theCheeese/Color-Pen-Reader/Presentations/Original Proposal Presentation.pptx

## AUTONOMOUS COLOR PEN READER

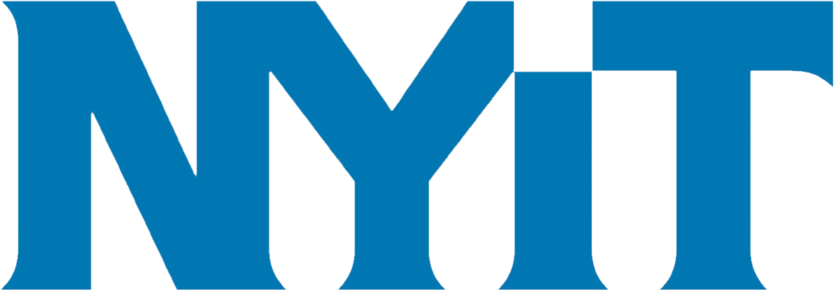
[picture p39: figure]

Capstone project proposal | Fall 2017

## 1. INTRODUCTION

1

Our members, motivations, significance and existing technologies

## Team members

MICHAEL MORDKOVICH (MISHA SYROV)
Project Manager/Software/Hardware Engineer

HAORAN WU (STEVEN WU)
Hardware/Software Engineer

KAIXIAN ZHU (ELLIS ZHU)
Software Engineer

OLUWADARASIMI ADENIYI (DARA ADENIYI)
Project Manager/Hardware Engineer/Researcher

Notes: This domain has controls around safeguarding assets. Some of the controls that this domain deals with are around the inventory of assets, ownership of assets, acceptable use of assets, return of assets.

It suggests controls around maintaining an inventory of assets and whether that inventory is current and kept up to date.

Also, it suggests that all information assets must have a clearly defined owner who is aware of their responsibilities.

It suggests that there be an acceptable use policy in place and there is process in place by which all employees are made aware of such policies.

## Existing technologies

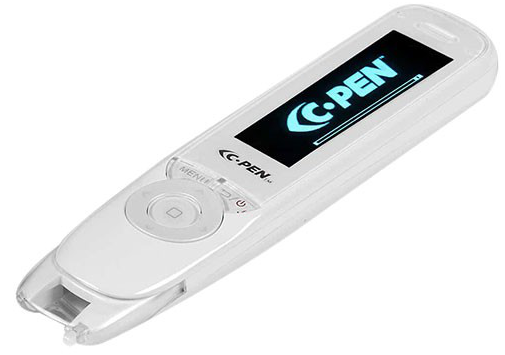
[picture p40: figure]
Resultado de imagem para cpen reader

- Existing technologies such as Scan marker and C-Pen don’t read colored text on colored backgrounds well

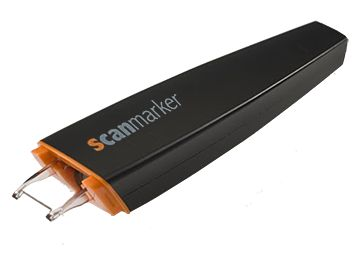
[picture p41: figure]
Resultado de imagem para scan marker logo

Notes: This domain has controls around safeguarding assets. Some of the controls that this domain deals with are around the inventory of assets, ownership of assets, acceptable use of assets, return of assets.

It suggests controls around maintaining an inventory of assets and whether that inventory is current and kept up to date.

Also, it suggests that all information assets must have a clearly defined owner who is aware of their responsibilities.

It suggests that there be an acceptable use policy in place and there is process in place by which all employees are made aware of such policies.

## 2. SOLUTION DEVELOPMENT

2

Solution proposal and plan of action

## Proposed solution

An electronic image processor that filters out the raw information from the pen reader's scanner

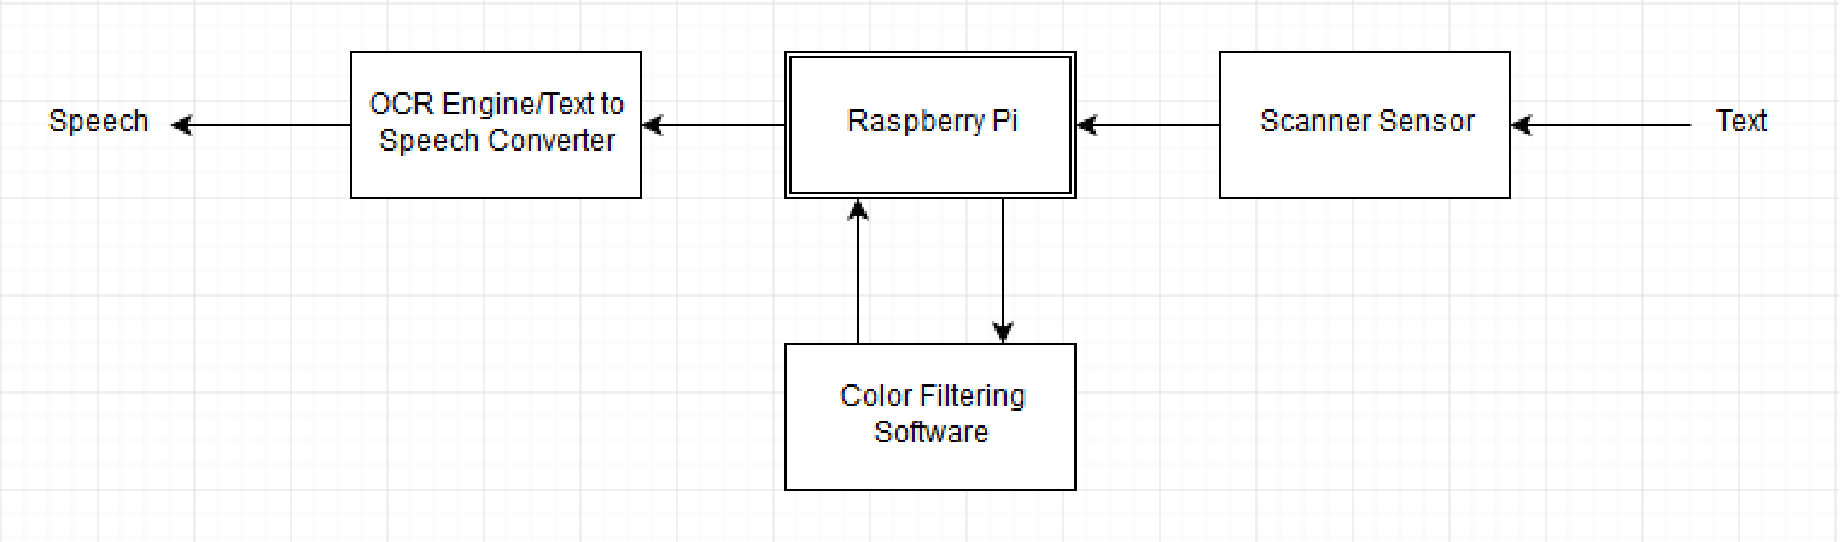
[picture p42: figure]

Notes: This domain has controls around safeguarding assets. Some of the controls that this domain deals with are around the inventory of assets, ownership of assets, acceptable use of assets, return of assets.

It suggests controls around maintaining an inventory of assets and whether that inventory is current and kept up to date.

Also, it suggests that all information assets must have a clearly defined owner who is aware of their responsibilities.

It suggests that there be an acceptable use policy in place and there is process in place by which all employees are made aware of such policies.

## Plan of action

Color filtering diagram:

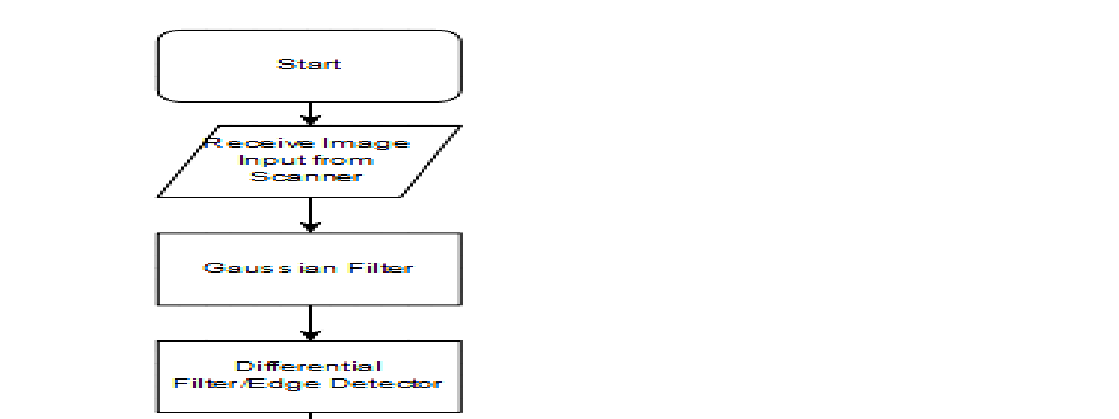
[picture p43: figure]
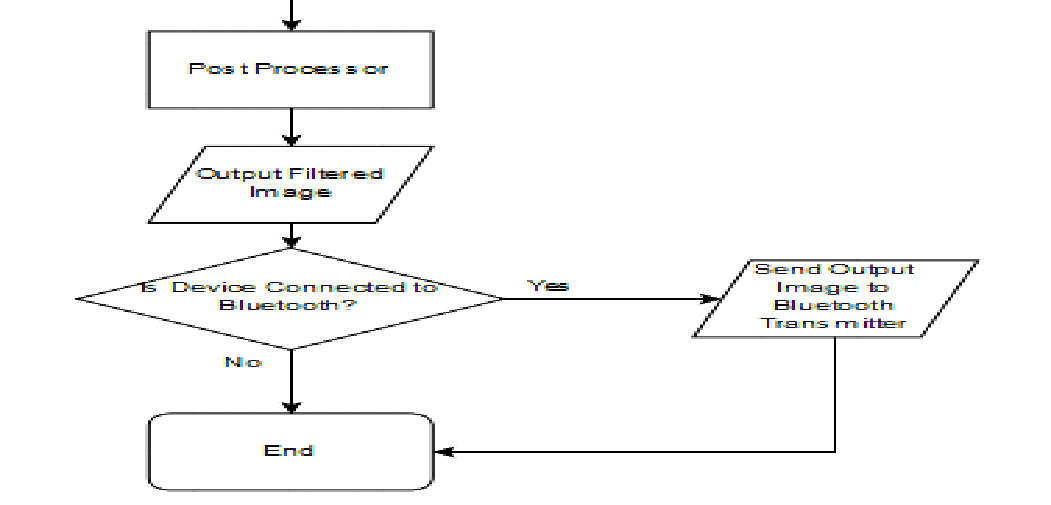
[picture p44: figure]

Notes: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

## Plan of action

Robotic Arm Control Diagram:

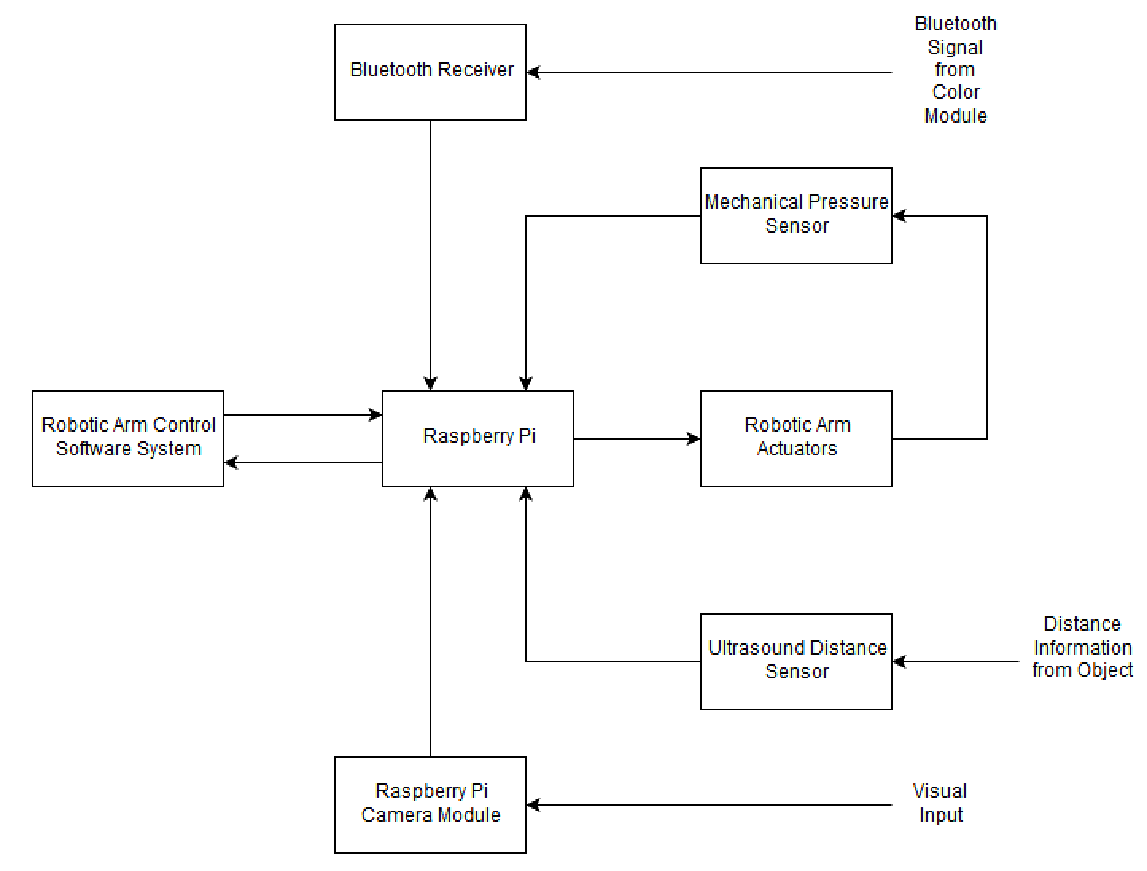
[picture p45: figure]

Notes: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

## Plan of action

Robot Arm Control Software Workflow:

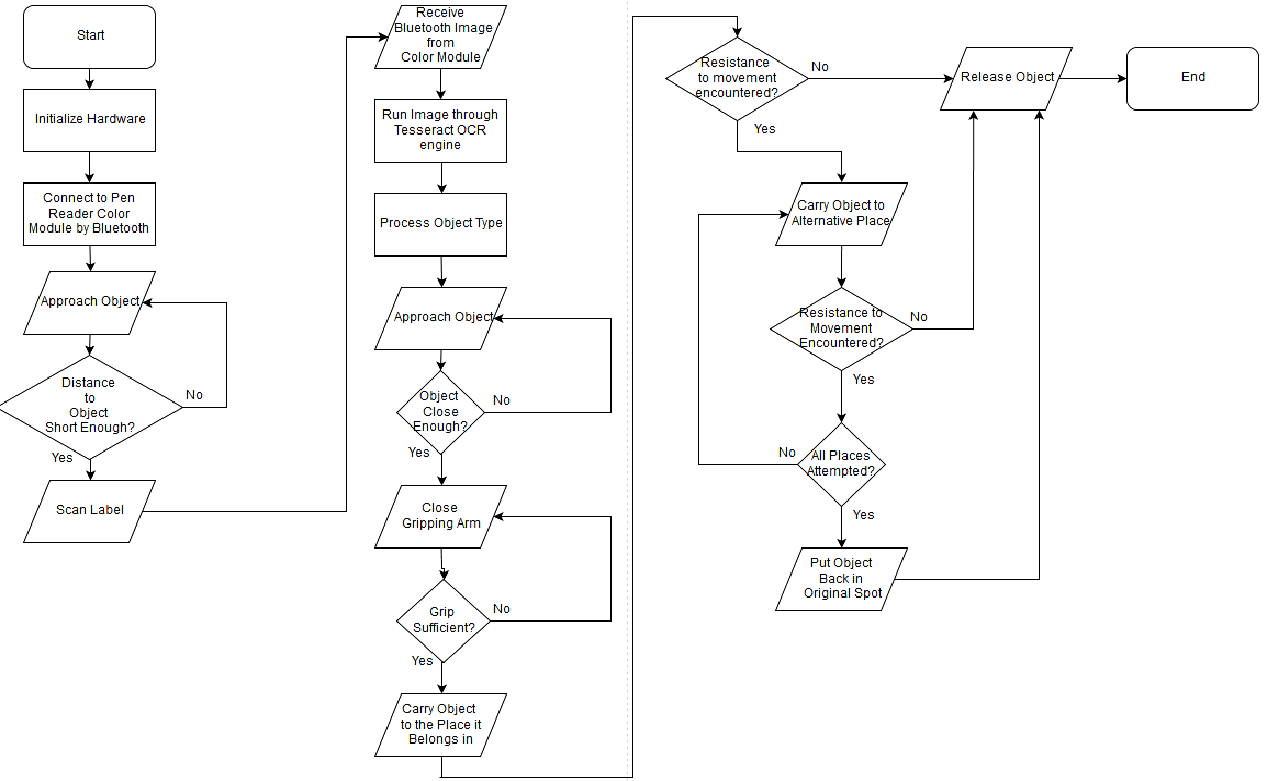
[picture p46: figure]

Notes: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

## Simulations

Input: Mixed colors, High, Medium & Low Resolution.

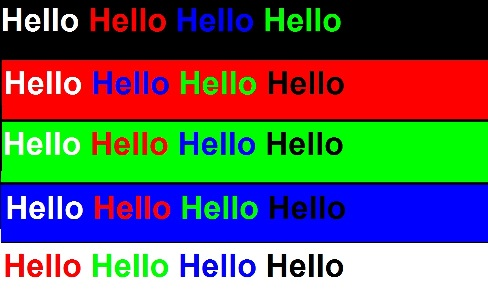
[picture p47: figure]
A close up of a screen Description generated with high confidence

Notes: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

## Simulations

Sobel Filter

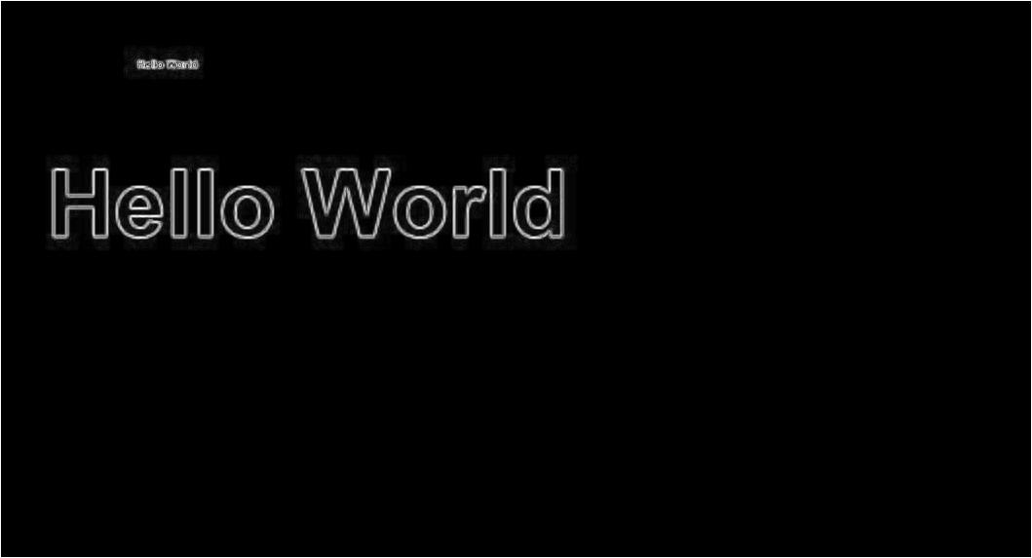
[picture p48: figure]
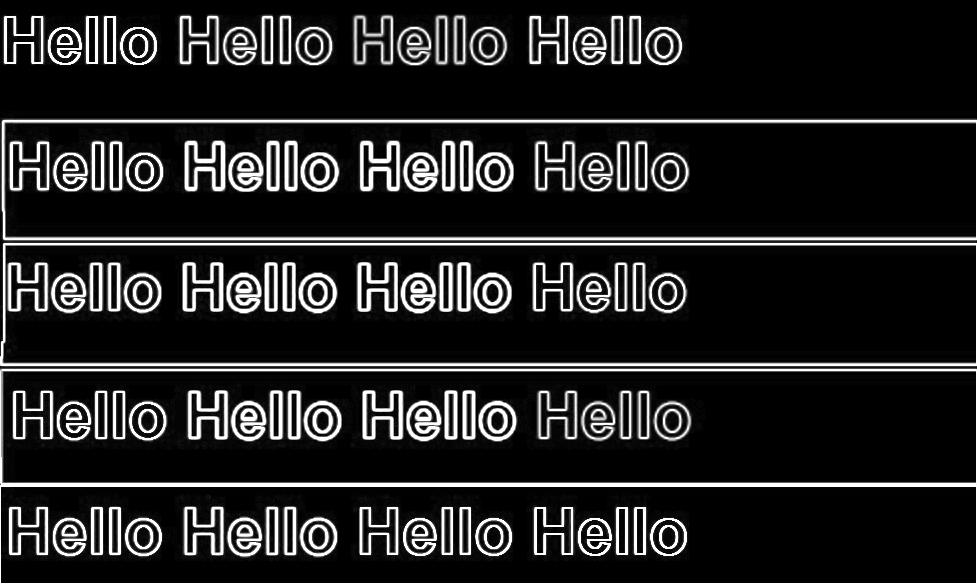
[picture p49: figure]
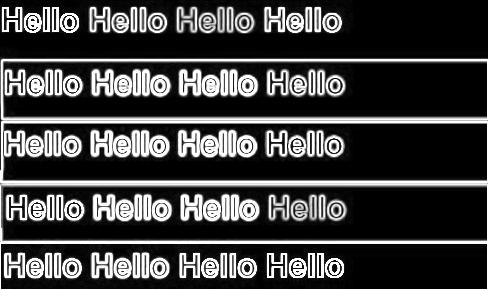
[picture p50: figure]
A screenshot of a cell phone Description generated with high confidence

Notes: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

## Simulations

Cosine Similarity Method

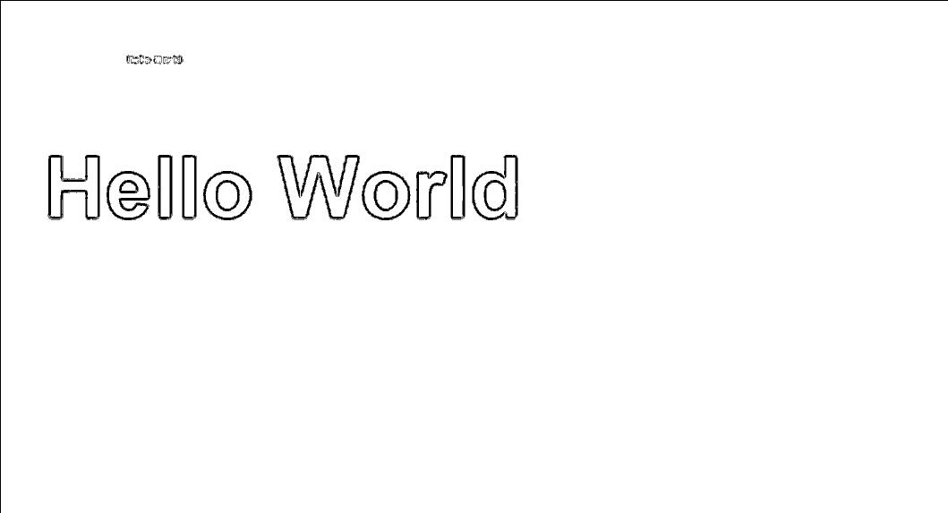
[picture p51: figure]
A screenshot of a cell phone Description generated with very high confidence
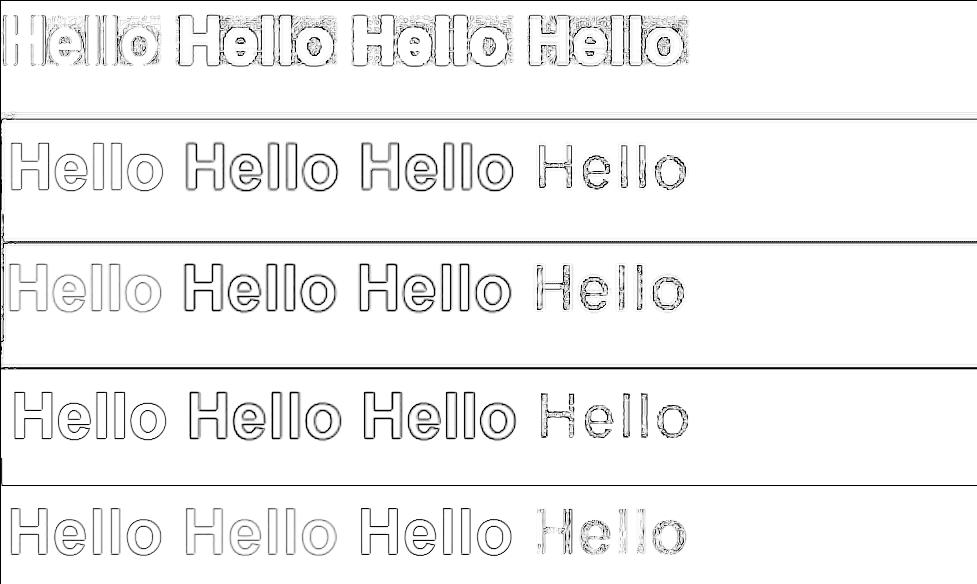
[picture p52: figure]
A screenshot of a cell phone Description generated with very high confidence
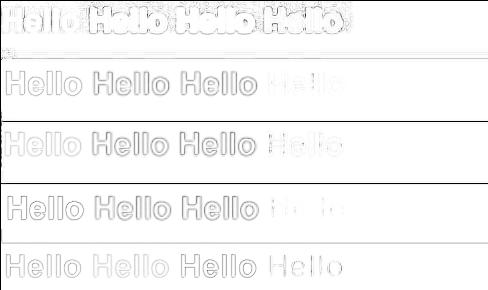
[picture p53: figure]
A screenshot of a cell phone Description generated with very high confidence

Notes: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

## Simulations

Canny and Sobel filters

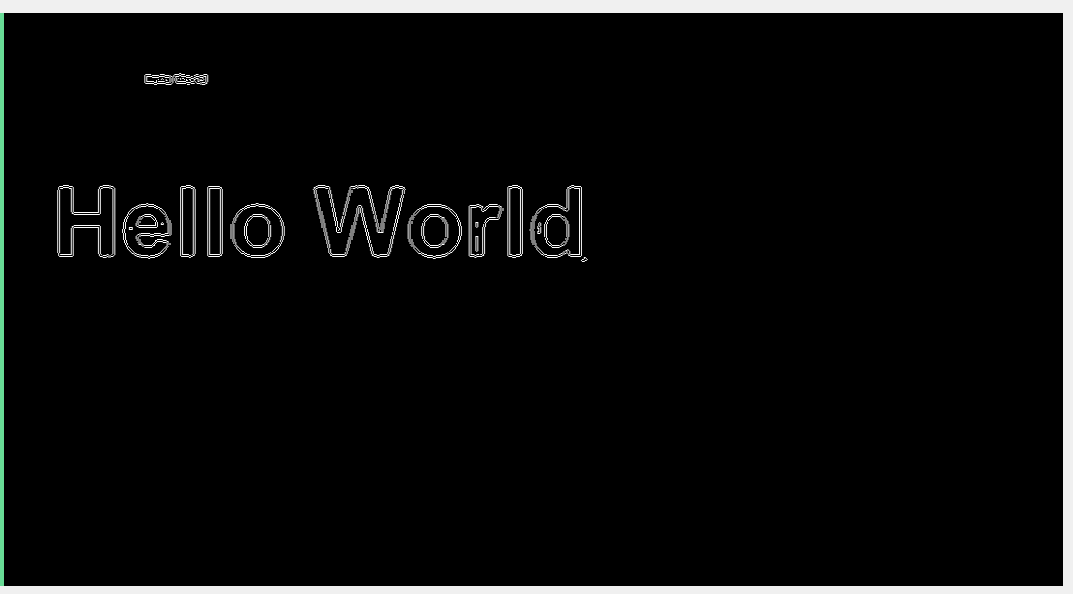
[picture p54: figure]
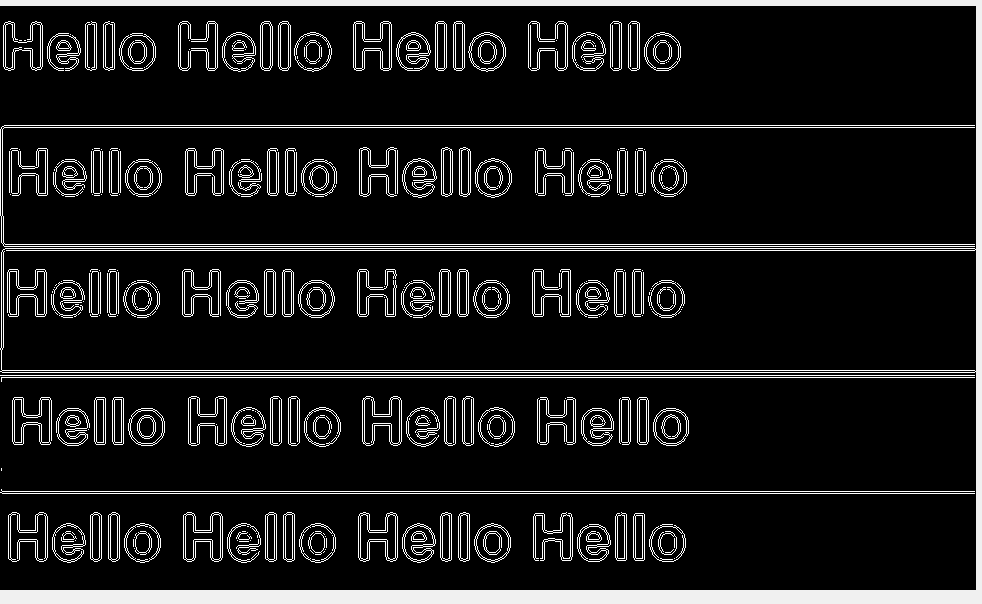
[picture p55: figure]
A picture containing text Description generated with high confidence
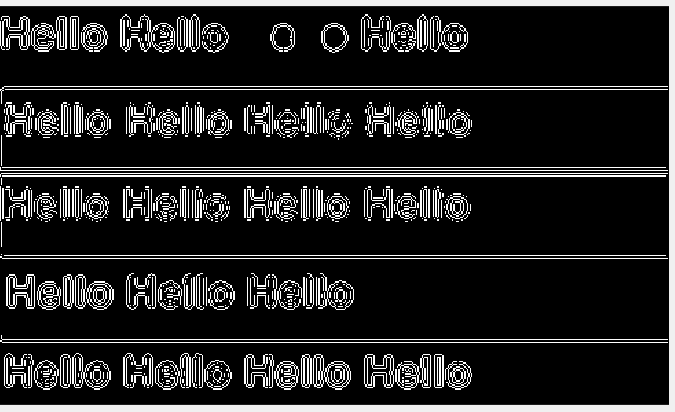
[picture p56: figure]
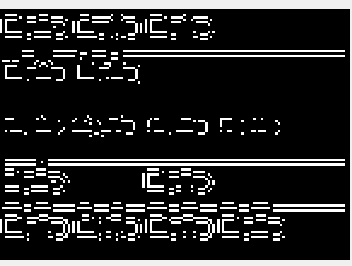
[picture p57: figure]

Notes: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

## Simulations

Canny Edge Detection Method

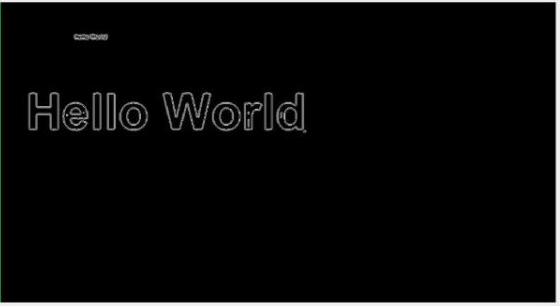
[picture p58: figure]
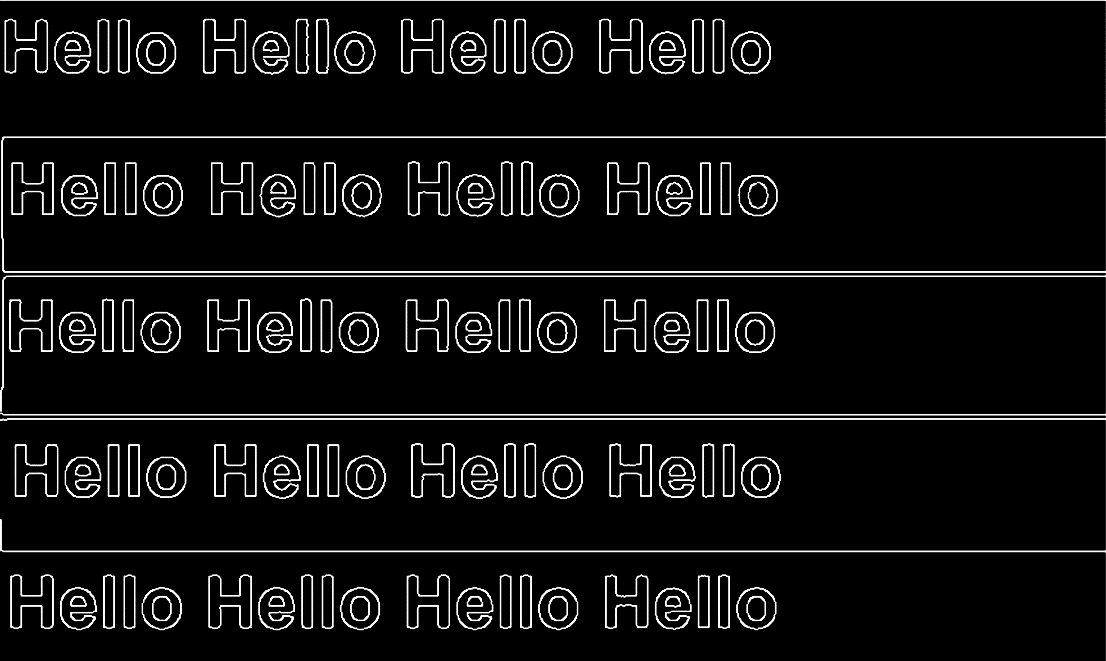
[picture p59: figure]
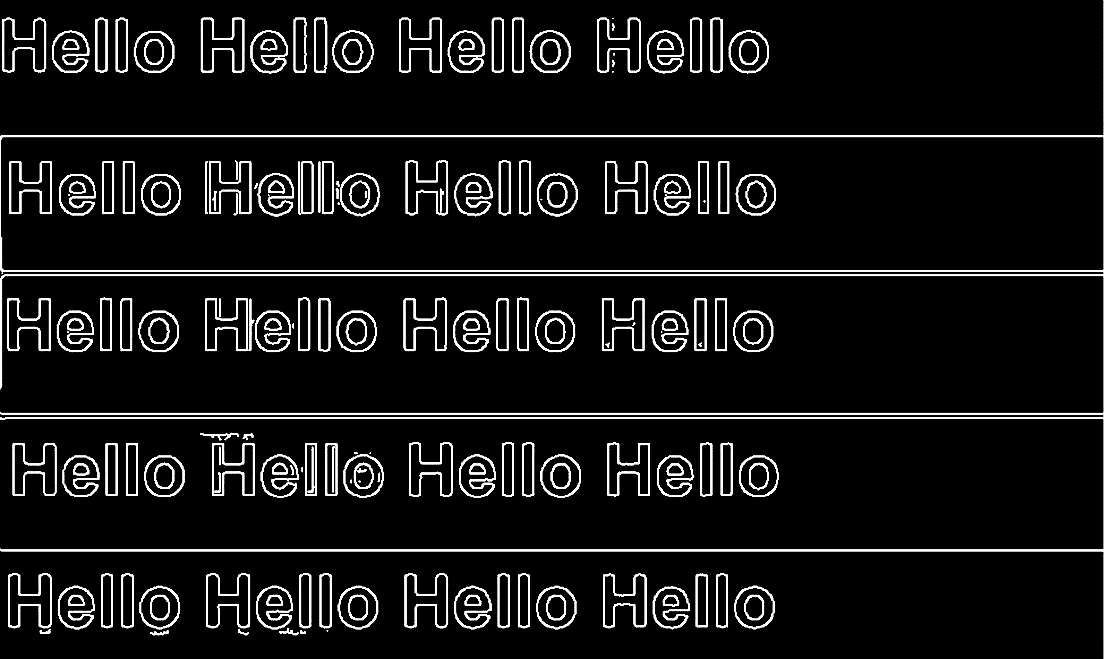
[picture p60: figure]
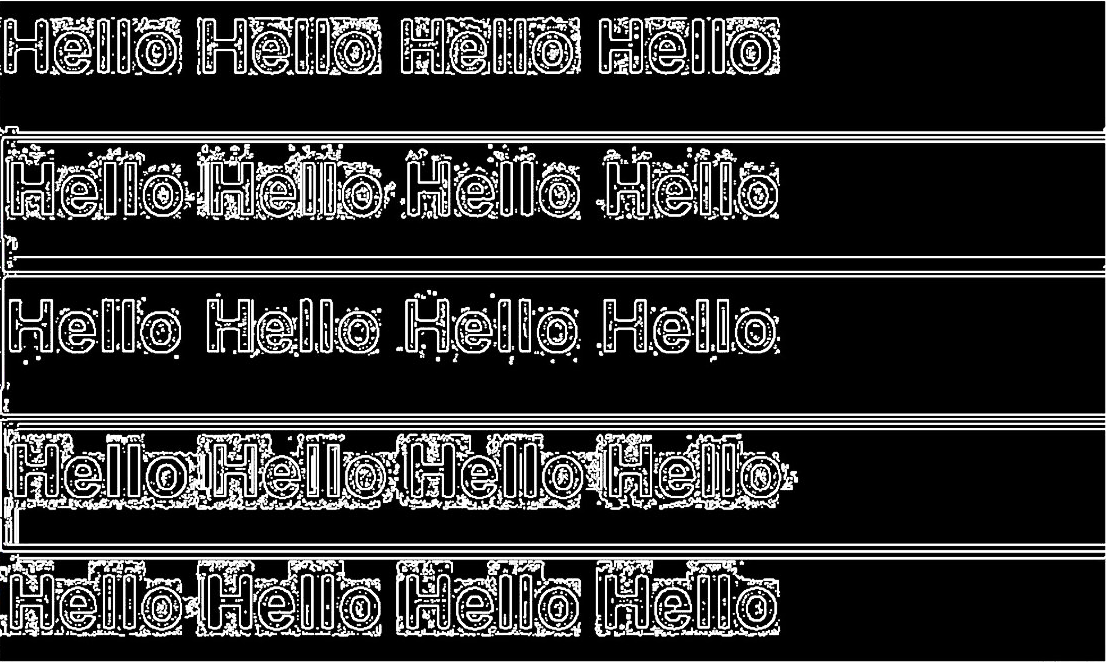
[picture p61: figure]

Notes: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

## Standard

The Bluetooth standard will be used to send images received by the pen reader to the robot arm wirelessly.
The chosen standard is
"IEEE 802.15.1: WPAN / Bluetooth"

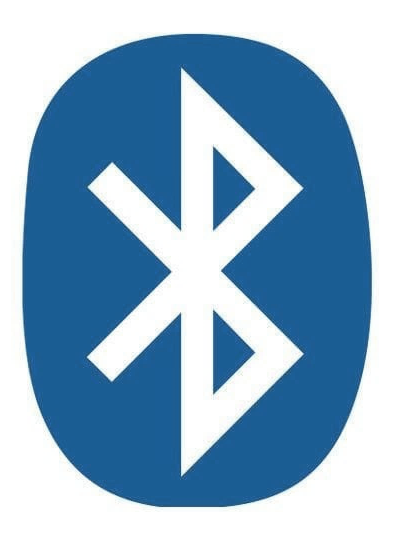
[picture p62: figure]
Resultado de imagem para bluetooth

Notes: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

## Commercialization

Features:
- Our improved reading pen is more convenient and a time saver compared to using a dictionary.
- There is no color limitation on characters you scan.
Action:
- Plan and implement BTL marketing activities to ask for feedback
Problems in Commercialization:
- How to carry out the business operations
- How to maximize the market acceptance

## Limitations and further development

- Limitation in recognizing several parallel character lines.
- We will try to restrict the scan area or improve the algorithm

- The pen uses red light, so it can’t be used in colorful materials.
- We will try to adapt the scanner to use white light, use filters or try a color-sensitive sensor

- The algorithm has low precision for hand-written characters.
- We will try to combine several OCR algorithms to enhance precision

- We haven’t got any technical document of our pen and we haven’t got the pen as well.

OCR technology

Pen

Recognition algorithm

Resource limitation

Notes: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

## 3. IMPACT

3

Ethical and societal impacts

## Impact

1. Our reading pen can help people with dyslexia
2. Our reading pen can help people who are visually impaired
3. People who are not familiar with English can also use this pen to help them work.
4. People who have disabilities in arm or hands can also use our reading pen to control some robotic arms to do some normal action.

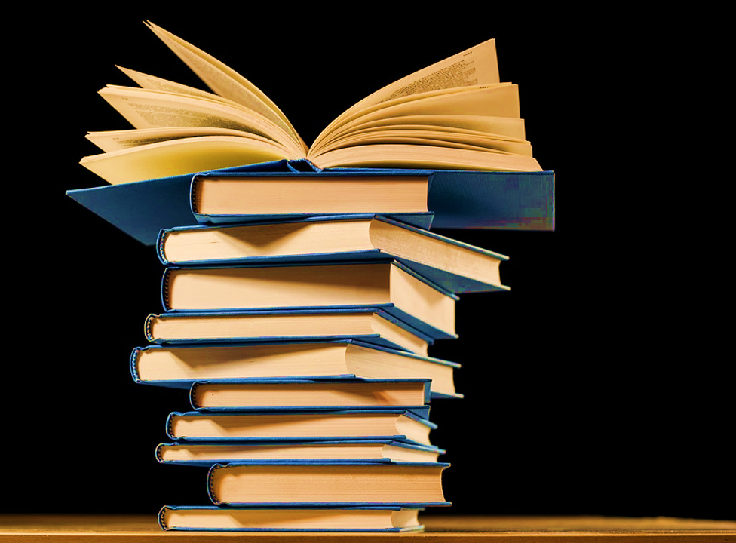
[picture p63: figure]

Notes: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

## References

[1] Siegel, Linda S. “Perspectives on Dyslexia.”, Paediatrics & Child Health 11.9 (2006): 581–587. Print.
[2] Bailey R. N., Indian R. W., Zhang X., Geiss L. S., Duenas M.R., Saaddine J. B. “Visual impairment and eye care among older adults—five states,” MMWR 2006; 55(49):1321–1325.
[3] Eikvil, Line. "OCR-Optical Character Recognition.", 1993.

Notes: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

## Thank you.
