theCheeese/Color-Pen-Reader/Presentations/Senior Design 2 Midterm Presentation.pptx

## AUTONOMOUS COLOR PEN READER


Capstone Project | Fall 2018

## 1. INTRODUCTION

1

Our members, motivations, significance and existing technologies

## Team members

MICHAEL MORDKOVICH (MISHA SYROV)
Project Manager/Software/Hardware Engineer

HAORAN WU (STEVEN WU)
Hardware/Software Engineer

KAIXIAN ZHU (ELLIS ZHU)
Software Engineer

OLUWADARASIMI ADENIYI (DARA ADENIYI)
Project Manager/Hardware Engineer/Researcher

Notes: This domain has controls around safeguarding assets. Some of the controls that this domain deals with are around the inventory of assets, ownership of assets, acceptable use of assets, return of assets.

It suggests controls around maintaining an inventory of assets and whether that inventory is current and kept up to date.

Also, it suggests that all information assets must have a clearly defined owner who is aware of their responsibilities.

It suggests that there be an acceptable use policy in place and there is process in place by which all employees are made aware of such policies.

## Motivation and significance

- Dyslexia affects up to 17% of general population[1];
- Around 3.4 million of US citizens are blind[2];
- Current pen readers have color limitation and only work in optimal conditions[3];

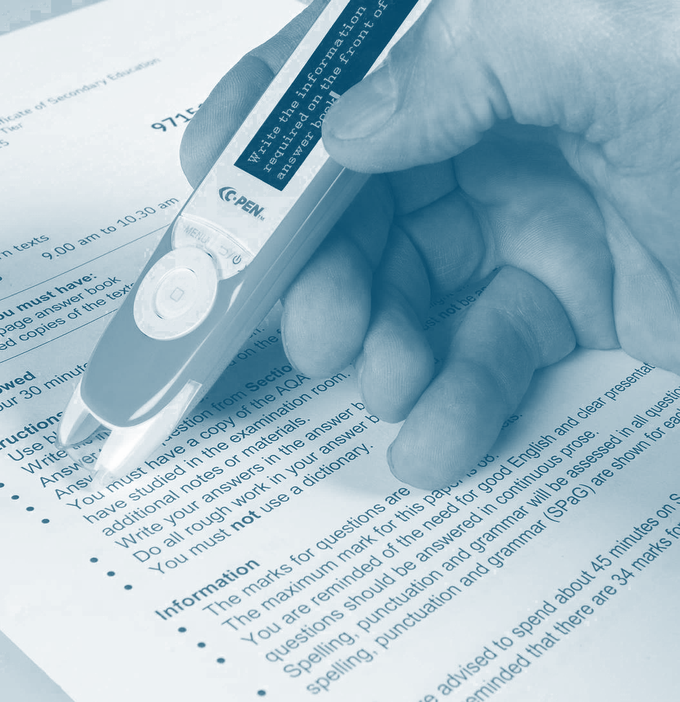
[picture p64: figure]
Resultado de imagem para pen reader

Notes: This domain has controls around safeguarding assets. Some of the controls that this domain deals with are around the inventory of assets, ownership of assets, acceptable use of assets, return of assets.

It suggests controls around maintaining an inventory of assets and whether that inventory is current and kept up to date.

Also, it suggests that all information assets must have a clearly defined owner who is aware of their responsibilities.

It suggests that there be an acceptable use policy in place and there is process in place by which all employees are made aware of such policies.

## Existing technologies

Resultado de imagem para cpen reader

- Existing technologies such as Scan marker and C-Pen don’t read colored text on colored backgrounds well

Resultado de imagem para scan marker logo

Notes: This domain has controls around safeguarding assets. Some of the controls that this domain deals with are around the inventory of assets, ownership of assets, acceptable use of assets, return of assets.

It suggests controls around maintaining an inventory of assets and whether that inventory is current and kept up to date.

Also, it suggests that all information assets must have a clearly defined owner who is aware of their responsibilities.

It suggests that there be an acceptable use policy in place and there is process in place by which all employees are made aware of such policies.

## 2. SOLUTION DEVELOPMENT

2

Solution proposal and plan of action

## Plan of action

Color filtering diagram:

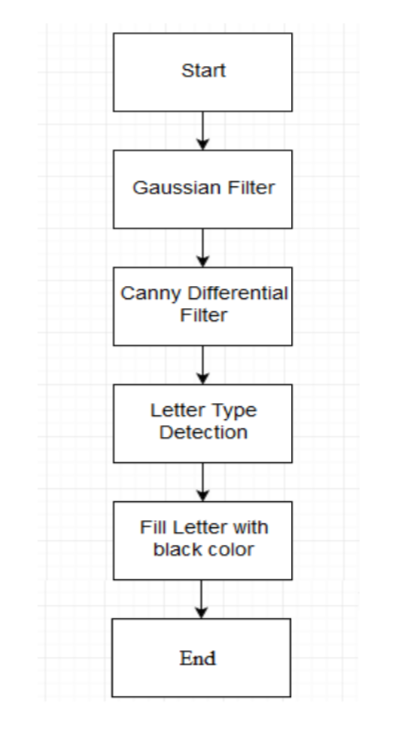
[picture p65: figure]

Notes: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

## Plan of action

High-level Software Design:

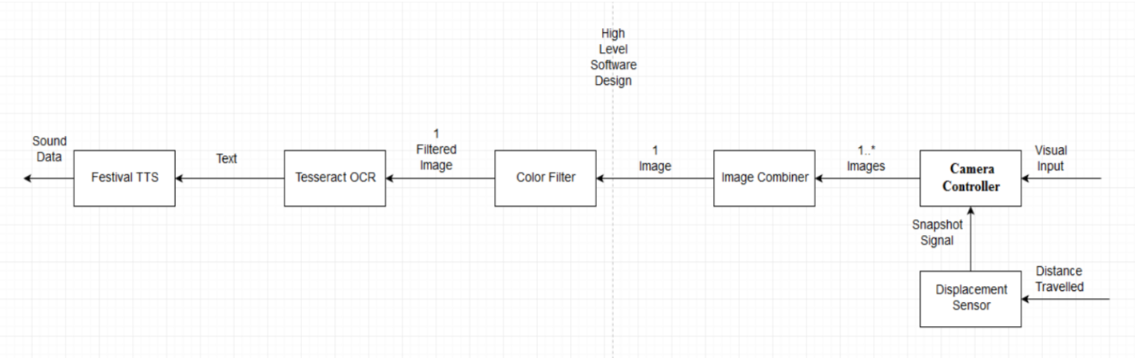
[picture p66: figure]

Notes: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

## Plan of action

High-level Hardware Design:

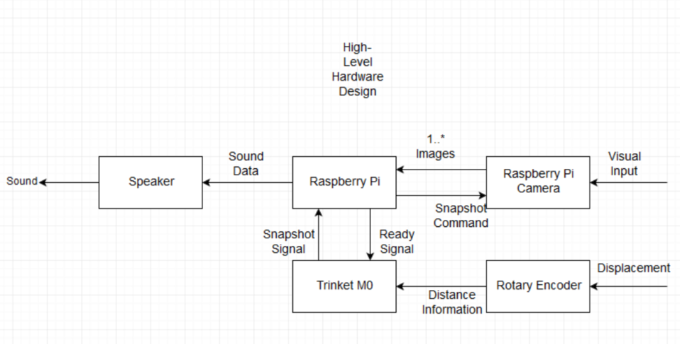
[picture p67: figure]

Notes: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

## Plan of action

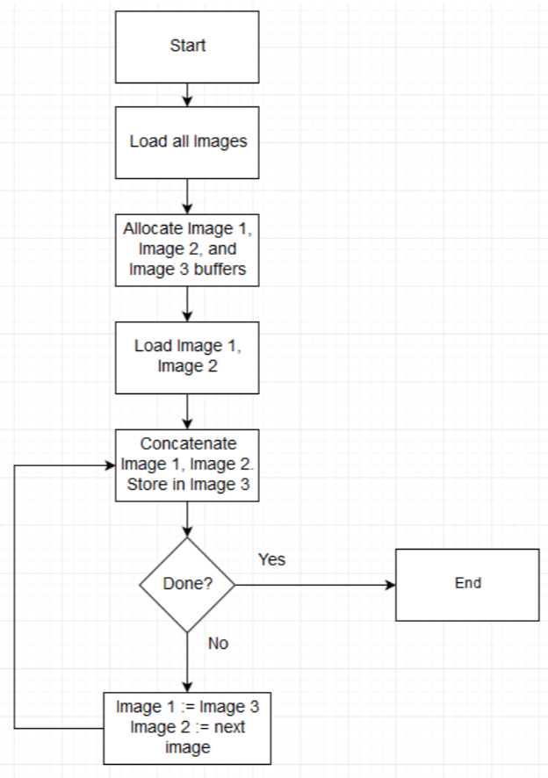
[picture p68: figure]

Image Combiner Design:

Notes: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

## Plan of action

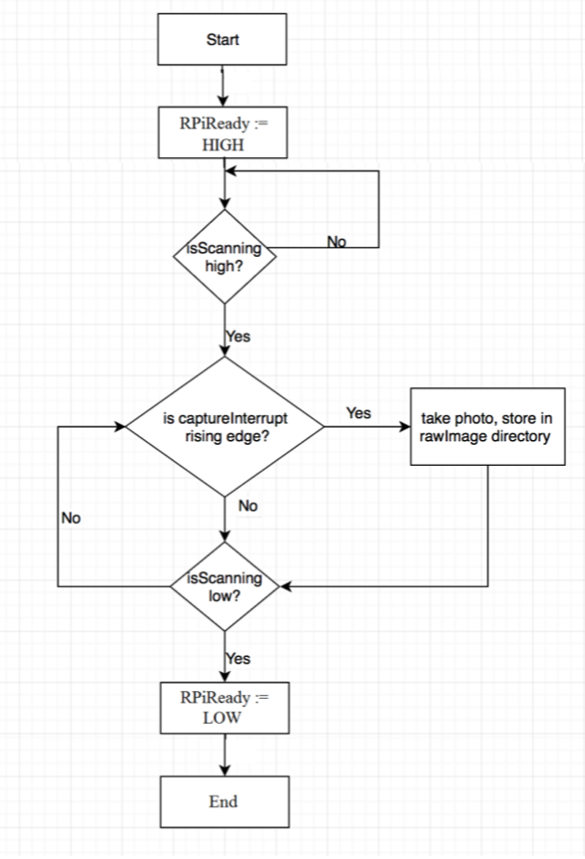
[picture p69: figure]

Camera Control Design:

Notes: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

## Plan of action

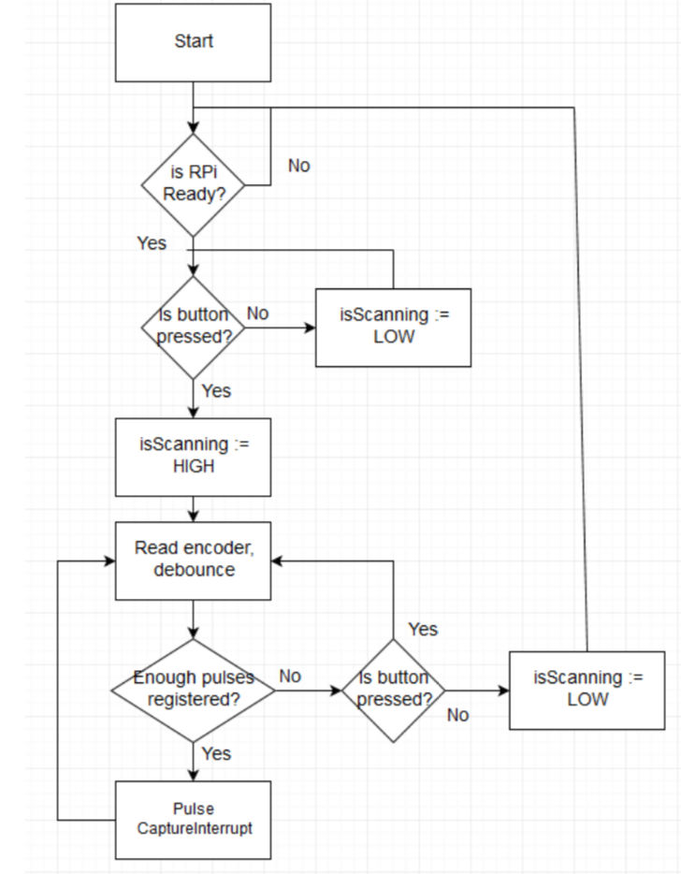
[picture p70: figure]

Closed-loop Feedback Design:

Notes: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

## Progress Made

- Matlab simulations & choosing color filter design
- Image Combiner algorithm
- Rotatory Encoder design
- Scanner design
- Combined each component
- Overcame hurdle by building pen instead of modifying

Notes: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

## Future Plan

- Week 1: Finish all software required for camera control and feedback
- Week 2: Design and assemble 3D enclosure for scanner
- Week 3: Present Project at CREAT symposium, finish tweaks in feedback system
- Week 4: Add battery, speaker, minor tweaking, fix bugs found during testing & present final prototype

Notes: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

## Commercialization

Features:
- Our improved reading pen is more convenient and a time saver compared to using a dictionary.
- There is no color limitation on characters you scan.
Action:
- Plan and implement BTL marketing activities to ask for feedback
Problems in Commercialization:
- How to carry out the business operations
- How to maximize the market acceptance

## Limitations and further development

- Limitation in recognizing several parallel character lines.
- We will try to restrict the scan area or improve the algorithm

- The pen uses red light, so it can’t be used in colorful materials.
- We will try to adapt the scanner to use white light, use filters or try a color-sensitive sensor

- The algorithm has low precision for hand-written characters.
- We will try to combine several OCR algorithms to enhance precision

- Small contrast between background and text may cause edge detector output to be faint making edge filling harder.
- Combine different methods of edge detection.

OCR technology

Pen

Recognition algorithm

Scanning module

Notes: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

## 3. IMPACT

3

Ethical and societal impacts

## Impact

1. Our reading pen can help people with dyslexia
2. Our reading pen can help people who are visually impaired
3. People who are not familiar with English can also use this pen to help them work.
4. People who have disabilities in arm or hands can also use our reading pen to control some robotic arms to do some normal action.


Notes: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

## Timeline

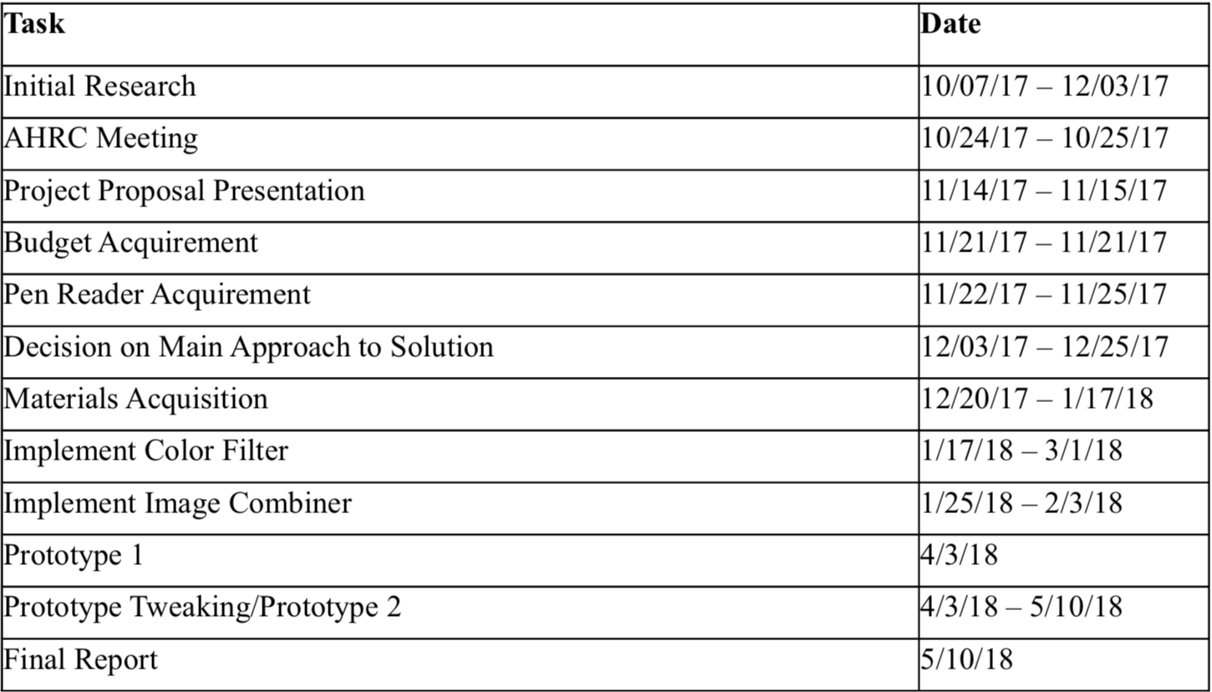
[picture p71: figure]

Notes: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

## References

[1] Siegel, Linda S. “Perspectives on Dyslexia.”, Paediatrics & Child Health 11.9 (2006): 581–587. Print.
[2] Bailey R. N., Indian R. W., Zhang X., Geiss L. S., Duenas M.R., Saaddine J. B. “Visual impairment and eye care among older adults—five states,” MMWR 2006; 55(49):1321–1325.
[3] Eikvil, Line. "OCR-Optical Character Recognition.", 1993.

Notes: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

## Thank you.
